MakersAsylumIndia/InfinityMirror/kicad/datasheets/IoT_lamp_12V_LED_01.png

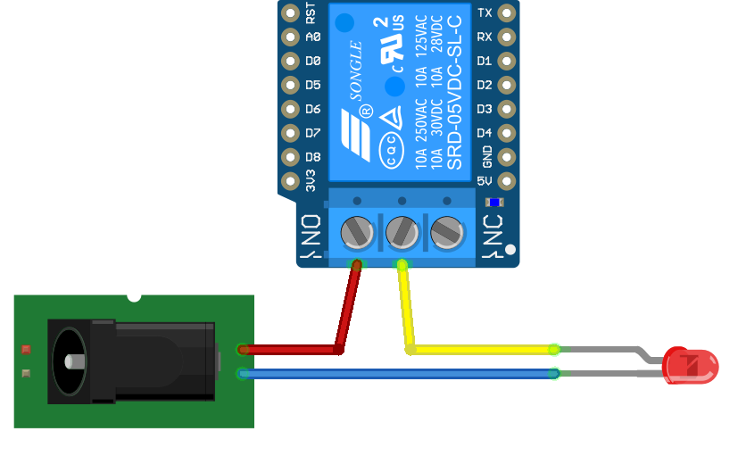
kicad/datasheets/IoT_lamp_12V_LED_01.png
