MakersAsylumIndia/InfinityMirror/fabricate/DXF_anool/mirror_2nos.dxf

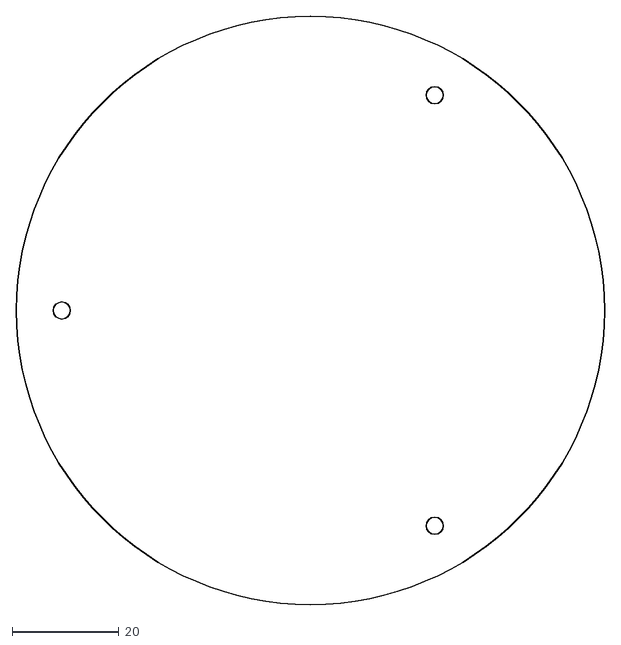
[picture p27: CAD file, 2022-07-25]
fabricate/DXF_anool/mirror_2nos.dxf
110.0 x 110.0
