MakersAsylumIndia/InfinityMirror/fabricate/DXF_SVG_kevin/arduino_micro_back.dxf

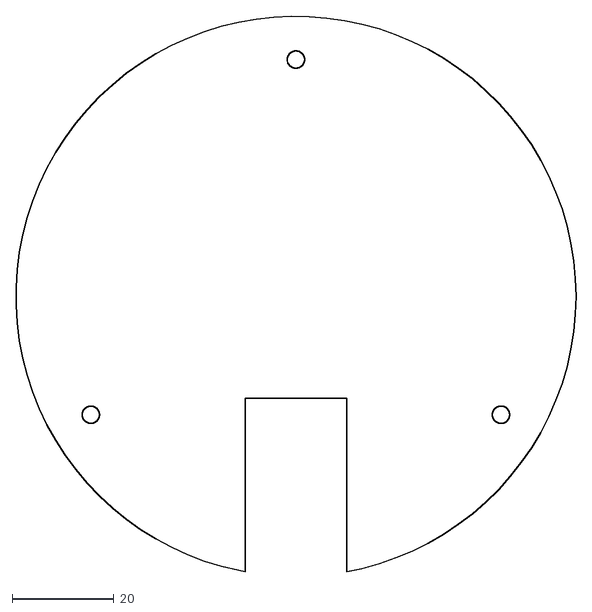
[picture p28: CAD file, 2022-07-25]
fabricate/DXF_SVG_kevin/arduino_micro_back.dxf
110.0 x 109.1
