MakersAsylumIndia/InfinityMirror/fabricate/arduino_nano.step

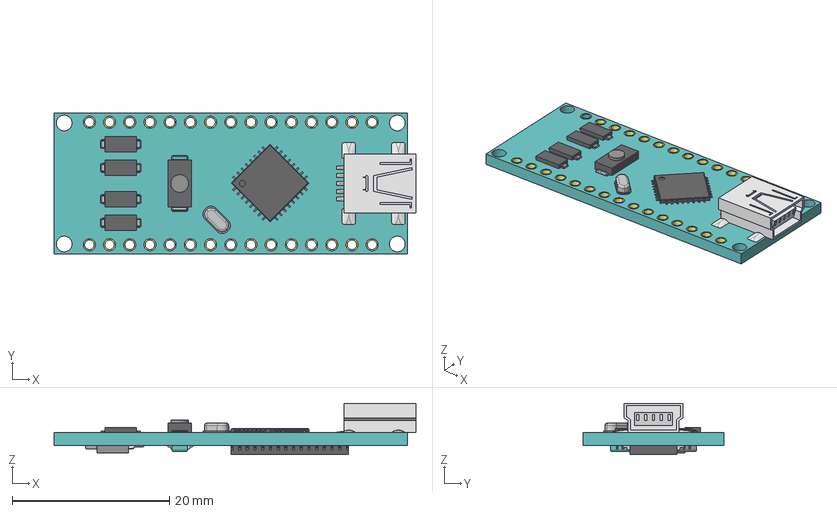
[picture p29: CAD file, 2022-07-25]
fabricate/arduino_nano.step
46.1 x 18.0 x 6.55 mm
USB
Component3(Mirror) x 16
Component5(Mirror) x 4
Component5(Mirror) (1) x 4
