MakersAsylumIndia/InfinityMirror/fabricate/DXF_anool/arduino_nano_back.dxf

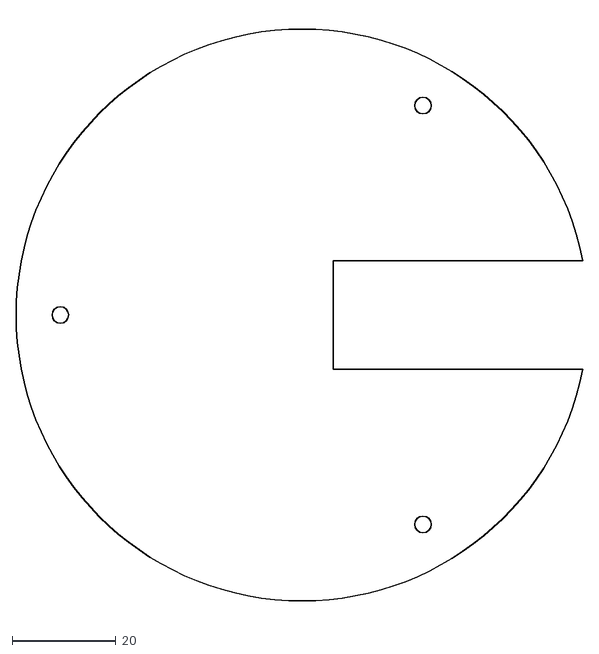
[picture p30: CAD file, 2022-07-25]
fabricate/DXF_anool/arduino_nano_back.dxf
109.0 x 114.9
