MakersAsylumIndia/InfinityMirror/fabricate/DXF_SVG_kevin/front_mirror.dxf

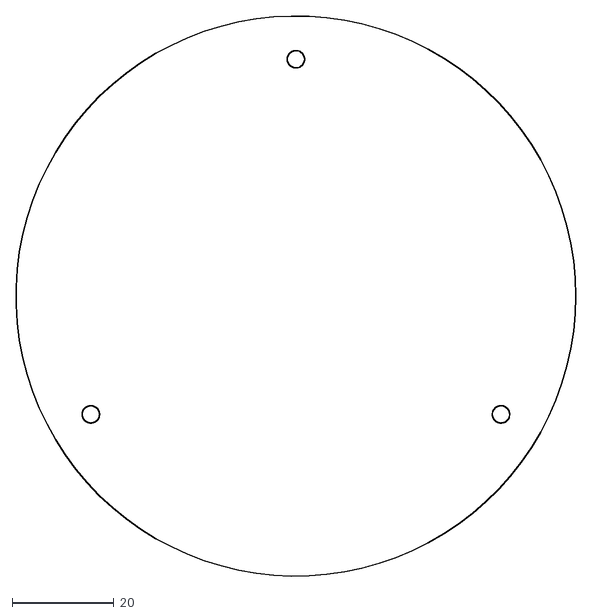
[picture p31: CAD file, 2022-07-25]
fabricate/DXF_SVG_kevin/front_mirror.dxf
110.0 x 110.0
