MakersAsylumIndia/InfinityMirror/fabricate/DXF_anool/arduino_micro_back.dxf

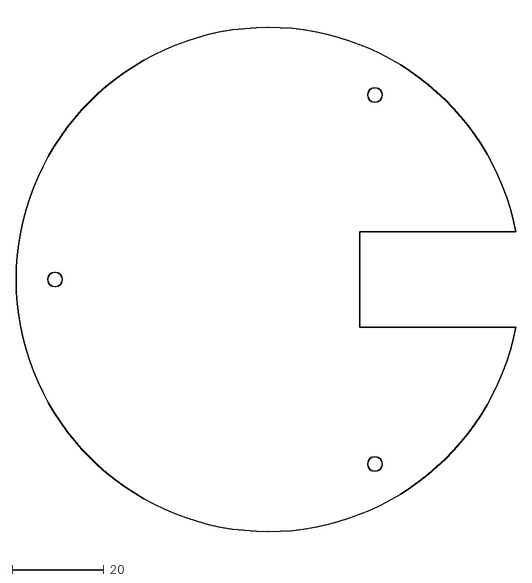
[picture p32: CAD file, 2022-07-25]
fabricate/DXF_anool/arduino_micro_back.dxf
109.0 x 114.9
