MakersAsylumIndia/InfinityMirror/fabricate/DXF_anool/back.dxf

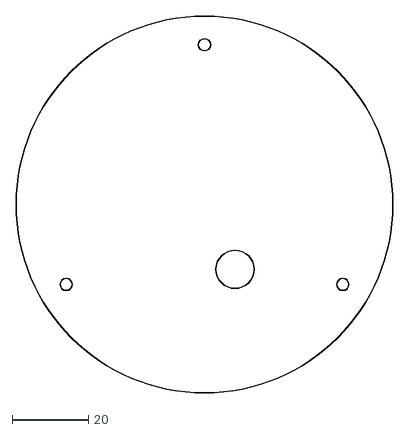
[picture p33: CAD file, 2022-07-25]
fabricate/DXF_anool/back.dxf
98.7 x 98.7
