MakersAsylumIndia/InfinityMirror/fabricate/Infinity_02_PDF/infinity_exploded_view.png

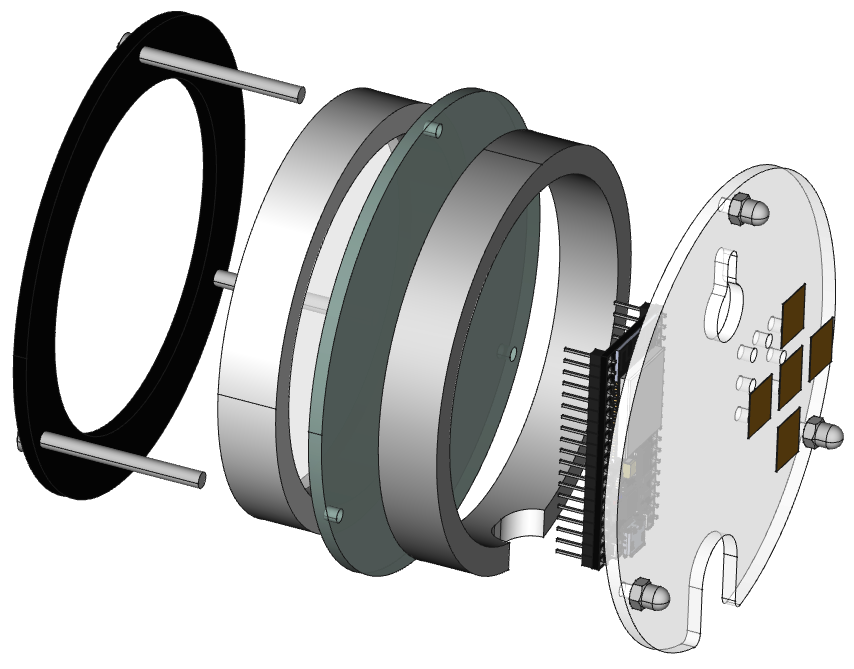
fabricate/Infinity_02_PDF/infinity_exploded_view.png
